bosd/Alpine/alpine/keymaps/bosd/config.h

/*
Copyright 2012 Jun Wako <wakojun@gmail.com>

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
You should have received a copy of the GNU General Public License
along with this program.  If not, see <http://www.gnu.org/licenses/>.
*/

#pragma once

#define MASTER_LEFT
//#define MASTER_RIGHT

//#define EE_HANDS

// wiring of the encoder
// #define NUM_ENCODERS 1
// #define ENCODER_RESOLUTION 4
#define ENCODERS_PAD_A { F4 }
#define ENCODERS_PAD_B { F5 }

#define RGBW
#define WS2812_DI_PIN B7
#define WS2812_BYTE_ORDER WS2812_BYTE_ORDER_GRB
